SolidHal/btrfly-keyboard/things/test.scad

difference () {
  union () {
    translate ([-65.26683897487581, 24.254647206382906, 2]) {
      cube ([10.2, 12, 4], center=true);
    }
  }
  union () {
    translate ([-65.26683897487581, 30.254647206382906, 5]) {
      rotate (a=90.0, v=[1, 0, 0]) {
        cylinder ($fn=30, h=20, r=2.55, center=true);
      }
    }
    translate ([-65.26683897487581, 23.254647206382906, 5]) {
      cube ([6.2, 10, 6], center=true);
    }
  }
}
